thom-heinrich/twinr/src/twinr/agent/personality/README.md

# personality

`personality` owns the typed evolving companion-state layer for `twinr.agent`.
It sits between long-term storage and base-agent prompting: the package defines
structured personality models, translates them into ordered prompt layers, and
now also owns the policy-gated background evolution path that persists signals
and current-state commits through remote-primary state.

## Responsibility

`personality` owns:
- define typed models for stable character, learned conversation style, humor, relationship context, continuity, place/world awareness, and reflection deltas
- build ordered prompt layers that preserve Twinr's legacy `SYSTEM` / `PERSONALITY` / `USER` contract
- mark authority-bearing `SYSTEM` / `PERSONALITY` prompt layers with trusted builder provenance so prompt-authority guards can distinguish them from contextual data
- render a bounded conversational self-expression and `MINDSHARE` layer so Twinr can naturally speak from ongoing themes without pretending to have a human inner life
- derive authoritative per-turn steering cues from shared-thread and appetite state so Twinr can decide more consistently when to briefly update, when one calm follow-up is acceptable, and when it should simply observe
- derive explicit per-topic positive-engagement actions such as `silent`, `hint`, `brief_update`, `ask_one`, and `invite_follow_up` so Twinr can foster welcomed interaction without becoming pushy
- derive calm ambient display-impulse candidates from that same structured state so Twinr's evolving tone, topics, co-attention, and memory-follow-up needs can surface visually outside spoken turns
- correlate shown reserve-card exposures with later structured turn evidence so the right-hand lane can feed back into the same bounded engagement model as spoken conversation
- classify shown-card reactions more precisely, including immediate pickup versus delayed pickup or visible pushback, so Twinr can remember not just whether a card landed but how directly it landed
- serialize those steering cues for runtime evaluators with compact semantic match summaries and region-qualified local titles where available, then resolve matched topics back into concrete follow-up keep-open versus release-after-answer behavior
- provide storage seams for remote current-state loading and saving without pushing persistence into base-agent prompting
- keep prompt-time snapshot reads read-only and current-head-only, so first live turns on the Pi never reopen legacy snapshot or pointer/blob probes on the critical path
- keep explicit prompt-time remote-read caps authoritative across nested current-head helpers, so supervisor/personality prompt loads cannot silently widen a 2-second hot-path budget back to cold bootstrap timeouts
- extract structured interaction, continuity, place, and world signals from long-term consolidation output and tool history
- gate background learning so repeated interaction, place, and world signals can evolve the durable personality snapshot without allowing one-off drift
- expose a narrow public engagement-signal read seam so non-prompt runtime consumers such as the ambient reserve bus can adapt from the same persisted state instead of rebuilding their own engagement view
- expose both synchronous commit paths and foreground-safe queueing paths so runtime turn finalization can hand off tool-history learning without blocking on remote-primary personality writes
- expose one explicit persisted-history probe seam so nightly/runtime operators can distinguish a truly readable zero-delta state from remote-blind or partially unreadable personality history
- manage RSS/Atom subscriptions plus calm refresh/discovery state for place/world intelligence
- learn slow-changing topic/region source-calibration signals from structured conversation and tool evidence
- condense repeated feed updates into situational-awareness threads so world context can mature over days/weeks instead of staying headline-shaped
- decay stale world and relationship context so Twinr stays situationally aware without becoming news-stuck or overfitting old preferences

`personality` does **not** own:
- provider-specific prompt copy or wording
- memory, reminder, automation, or graph persistence implementations
- foreground runtime loop decisions about which dynamic sections belong to tool, supervisor, or main turns
- the fast supervisor lane's final prompt selection and routing policy

## Key files

| File | Purpose |
|---|---|
| [models.py](./models.py) | Typed evolving-personality state and prompt-layer models |
| [_payload_utils.py](./_payload_utils.py) | Shared payload normalization helpers reused by `models.py` and `intelligence/models.py` so remote-state decoding stays aligned |
| [context_builder.py](./context_builder.py) | Ordered prompt-layer assembly |
| [self_expression.py](./self_expression.py) | Conversational self-expression policy plus prompt-facing current-mindshare rendering |
| [_display_utils.py](./_display_utils.py) | Shared text normalization, truncation, and deterministic variation helpers for ambient display copy/candidate generation |
| [display_impulse_copy.py](./display_impulse_copy.py) | Deterministic fallback copy for ambient display impulses that keeps the large headline explanatory and the smaller second line as the CTA when the bounded reserve-lane LLM rewrite is unavailable |
| [display_impulses.py](./display_impulses.py) | Silent ambient display-impulse candidates derived generically from mindshare and positive-engagement state, including structured generation context, semantic `card_intent` blocks for reserve-card rewriting, and a generic candidate-family label for reserve-bus planning mix |
| [ambient_feedback.py](./ambient_feedback.py) | Correlate shown reserve-card exposures with later structured turn evidence and turn those reactions into generic engagement signals |
| [positive_engagement.py](./positive_engagement.py) | Explicit positive-engagement actions derived generically from appetite, ongoing interest, and co-attention |
| [steering.py](./steering.py) | Authoritative turn-steering cues plus runtime follow-up resolution derived from co-attention and conversation appetite |
| [profile_defaults.py](./profile_defaults.py) | Shared baseline style/humor profiles used by the runtime evolution loop and evaluation tooling |
| [_remote_state_utils.py](./_remote_state_utils.py) | Shared remote-primary adapter resolution used by the personality and world-intelligence snapshot stores |
| [store.py](./store.py) | Remote current-head/item persistence seam for personality snapshot state, signals, and deltas; prompt-time loads stay read-only and current-head-only so live voice turns do not reopen legacy snapshot probes |
| [evolution.py](./evolution.py) | Policy-gated background learning loop, contradiction/sensitivity gates, and decay maintenance |
| [signals.py](./signals.py) | Structured signal taxonomy plus extraction for style, humor, topic, continuity, place, and world evidence |
| [learning.py](./learning.py) | Runtime-facing bridge from extracted signals into background evolution |
| [service.py](./service.py) | Prompting-facing integration service plus the public read seam for persisted engagement signals used by the ambient reserve bus; short-lived caches key on stable remote-state identity so capped-timeout clones do not replay the same remote reads every turn |
| [intelligence/](./intelligence) | RSS/world-intelligence subscriptions, calibration signals, reflection-phase recalibration, and refresh-to-world-signal conversion |
| [component.yaml](./component.yaml) | Structured package metadata |
| [AGENTS.md](./AGENTS.md) | Local invariants and verification |

## Usage

```python
from twinr.agent.personality import PersonalityContextService

service = PersonalityContextService()
sections = service.build_static_sections(
    legacy_sections=(("SYSTEM", "Base system"), ("PERSONALITY", "Base style")),
    config=config,
    remote_state=remote_state,
)
```

```python
from twinr.agent.personality import (
    PersonalityLearningService,
)

learning = PersonalityLearningService.from_config(config, remote_state=remote_state)
result = learning.record_tool_history(
    tool_calls=(tool_call,),
    tool_results=(tool_result,),
)
```

```python
learning.enqueue_tool_history(
    tool_calls=(tool_call,),
    tool_results=(tool_result,),
)
# later, one background commit path flushes the queued signals
learning.flush_pending()
```

## Learning model

The current signal taxonomy is intentionally structured and conservative:

- `topic_affinity` and `topic_aversion` shape relationship salience only after repeated support
- `verbosity_preference` and `initiative_preference` update a separate conversation-style profile instead of rewriting core traits
- `humor_feedback` may move humor intensity slowly, but sensitive-context turns never reinforce humor upward implicitly
- `thread` summaries refresh continuity directly and expire over time
- `world` signals are freshness-bound and decay out of the prompt once stale
- RSS-backed world intelligence is separate from ad-hoc live search: discovery is occasional and explicit, calibration learns slowly from structured conversation/tool evidence, refresh is cadence-bound, and feed items become contextual `WORLD`/`CONTINUITY` updates plus slower situational-awareness threads
- Twinr's conversational self-expression stays bounded: it may speak from `MINDSHARE` when the user invites open conversation or asks what Twinr has been following, but it must not invent secret emotions, private off-screen experiences, or human-like inner life
- `MINDSHARE` surfacing stays generic and data-driven: selection may vary slightly via bounded stochasticity, but it must be based on source type and salience rather than hardcoded entity names or place-first special cases
- repeated user engagement with one topic may boost how often matching mindshare items surface and how strongly the RSS intelligence layer continues to watch that topic, but this must remain bounded and evidence-driven
- explicit structured reactions like follow-up requests may raise topic engagement faster than passive affinity, but the signal must stay typed and auditable
- boosted topic engagement must decay over time and let RSS tuning fall back to baseline when the user stops leaning into that topic
- Twinr's engagement model distinguishes `resonant`, `warm`, `uncertain`, `cooling`, and `avoid`; absence alone must not count as dislike unless repeated prior exposure and non-reengagement are structurally evidenced
- topics currently classified as `avoid` must be suppressed from surfaced `MINDSHARE`, not merely scored lower, so explicit back-off signals cannot leak into prompt context
- `MINDSHARE` now also derives a topic-specific `conversation appetite` from those engagement states plus the learned global style profile, so each surfaced theme carries bounded cues for `depth`, `follow-up`, and `proactivity` instead of relying on hidden prompt guesswork
- `positive_engagement.py` lifts that implicit guidance into explicit turn actions: each surfaced topic resolves generically to `silent`, `hint`, `brief_update`, `ask_one`, or `invite_follow_up`, and the policy must stay topic-generic instead of accreting hardcoded examples
- `display_impulses.py` and `display_impulse_copy.py` reuse the same generic state for non-voice ambient display moments: reserve-card candidates must stay positive and generic, with an explanatory headline plus a separate CTA line instead of hardcoding specific places, topics, or benchmark phrases
- the ambient display lane may also surface a fresh continuity thread as one calm `hint` card before durable user engagement has fully formed, because the reserve bus is a lower-pressure surface than a spoken turn; `cooling` and `avoid` topics must still stay out
- reserve-card candidates should stay companion-like rather than search-box-like: raw `live_search` residue may still shape durable engagement state, but it should not surface directly as a visible right-lane opener
- `display_impulses.py` now also carries one generic `candidate_family` plus semantic `card_intent` per reserve-card candidate so the right-hand bus can mix world/place/memory/social families without ad-hoc named-topic spacing rules and the LLM rewrite step can write from structured meaning instead of only phrase-like anchors
- ambient reserve-card copy should make the headline itself explain the topic and use the smaller second line as the CTA, while still carrying one clear topical anchor so the user immediately knows which thread Twinr wants to open
- ambient reserve-card copy may also surface calm memory-improving prompts such as open-thread follow-ups, clarifying questions, or consistency checks, but only when those come from structured durable state rather than ad-hoc string hacks
- reserve-lane generation should receive generic structured context for those memory or shared-thread prompts, so the visible wording can stay natural and personality-shaped instead of echoing raw topic labels
- `self_expression.py` and `display_impulses.py` should hand reserve generation the real thread/topic summary itself, not internal English scaffolding like durable-attention wrappers, so visible German copy can stay grounded in the actual topic instead of paraphrasing implementation noise
- shown reserve cards now participate in the same generic engagement loop: later structured turn evidence may resolve one card into pickup, cooling, aversion, or repeated non-pickup, and those outcomes flow back through the normal personality/world-intelligence evolution path
- immediate shown-card pickup should count as stronger positive evidence than a much later return, and the structured feedback path may also emit a short-lived reserve-bus feedback hint so the same-day display plan can adapt faster without hardcoding topics in the runtime loop
- repeated user returns to a topic may also raise Twinr's persisted `ongoing interest` in it; this is the companion analogue of `stop/linger/return` signals in ranking systems, but bounded for dignity and calm rather than optimized for addiction or time-on-device
- when sustained user interest and Twinr's own feed coverage line up, the system now also tracks bounded `co-attention` so some themes can become genuine shared running threads rather than isolated prompt hints
- `steering.py` turns that same state into authoritative turn guidance inside `PERSONALITY`, serializes compact machine-readable cues for the closure evaluator, and resolves matched topics back into concrete runtime follow-up behavior without turning `MINDSHARE` itself into instruction authority
- steering cues should stay semantically narrow: if a durable signal already says a topic is local/regional and region-scoped, the cue title may carry that regional anchor so closure matching does not confuse nearby community topics with public-policy threads
- the fast supervisor lane should consume only a lean subset of this package: stable character/style may flow there, but volatile layers such as `MINDSHARE`, `CONTINUITY`, `PLACE`, `WORLD`, and `REFLECTION` must stay out so noisy search routing does not get semantically dragged by ambient state

## See also

- [component.yaml](./component.yaml)
- [AGENTS.md](./AGENTS.md)
- [../base_agent/prompting/README.md](../base_agent/prompting/README.md)
- [../../../../docs/persistent_personality_architecture.md](../../../../docs/persistent_personality_architecture.md)
