thom-heinrich/twinr/src/twinr/agent/base_agent/runtime/README.md

# runtime

`runtime` owns the canonical `TwinrRuntime` object for the base agent. It
assembles focused mixins for lifecycle setup, state transitions, provider
context, structured memory, guided user-discovery, reminders and automations,
and runtime snapshot durability.

## Responsibility

`runtime` owns:
- compose `TwinrRuntime` from focused mixins
- bootstrap and shut down runtime-owned stores and services
- honor the configured required-remote readiness contract during bootstrap, including trusting the external watchdog artifact in Pi `watchdog_artifact` mode instead of forcing a second deep remote probe
- drive state transitions for listening, answering, printing, and failures
- rearm follow-up listening directly from `answering` when a conversation stays open after a spoken reply
- also permit the delayed `waiting -> listening` reopen that occurs when speech has already ended but the follow-up closure gate resolves a moment later
- collapse transcript-first provisional `tts_finished + follow_up_rearmed` into one persisted `listening` snapshot when the remote follow-up window is already open, so the visible Pi surface does not pay two back-to-back runtime writes before leaving `answering`
- assemble provider-facing context, adaptive timing, voice guidance, and active guided-discovery state hints for tool-capable turns
- normalize legacy voice-status labels before provider guidance so low-risk discovery turns do not accidentally fall back to conservative unknown-speaker wording
- surface the currently visible reserve-lane card as bounded grounding context for supervisor/search lanes when the user is clearly reacting to what Twinr is showing, including a stronger per-turn authoritative overlay for fast supervisor decisions
- keep the first-word lane on bounded local context so direct replies never block on remote long-term retrieval
- keep the supervisor fast lane on the same remote-free path while still surfacing one local on-device memory summary
- keep runtime-local tool turns on a bounded tiny-recent context when broader long-term memory is not needed, so status/control handoffs do not block the streaming final lane on remote retrieval
- keep tool-context guided-discovery hints on one local prompt-safe status snapshot, so live voice turns never trigger authoritative remote discovery reads just to build a system hint
- emit provider-context stage metrics and one explicit remote-context decision trace when workflow forensics bind runtime trace hooks, so slow `tool_provider_conversation_context()` turns can be attributed to lock snapshot, discovery, long-term retrieval, or final message assembly instead of appearing as one opaque blob
- mediate on-device memory, durable memory, reminders, automations, and snapshots
- expose explicit durable-memory reads from the prompt-context store so later recall of `remember_memory` facts has a runtime-owned read path, not only hidden prompt assembly
- restore persisted runtime status through the state-machine snapshot contract instead of assigning to the read-only runtime `status` property, so startup restore can reinstate only the safe idle `waiting` state plus any orthogonal `printing_active` flag without false warnings while refusing to resurrect stale non-idle or `error` statuses from older process lifetimes
- let `state.RuntimeSnapshotStore` remain the authoritative cross-process snapshot lock so Pi runtimes with `portalocker` installed do not self-deadlock by taking the same lock file twice during restore/persist
- expose reminder-reservation release semantics so workflow races can unwind a reserved reminder before speech starts without forcing a fake failure retry delay
- expose the runtime-side guided user-discovery flow so Twinr can persist, review, correct, and delete high-value get-to-know-you facts across managed context, graph memory, and durable memory without bloating orchestration code
- expose active self-coding dialogue and compile-job guidance to the tool lane so follow-up answers and activation requests can reuse runtime-owned `session_id` / `job_id` state instead of asking the user for internal identifiers
- forward completed tool history into long-term-backed personality learning after a turn is finalized
- keep the explicit best-effort `flush_long_term_memory()` API bounded to the caller's timeout while reserving the stricter remote-primary minimum only for long-term object/graph/midterm durability paths, not already-attested prompt-context writes
- expose runtime-side RSS/world-intelligence configuration so persistent feed subscriptions can shape Twinr's calm place/world awareness
- own the bounded temporary voice-quiet window so Twinr can suppress transcript-first wake and automatic follow-up for a user-requested period without changing the button/manual path

`runtime` does **not** own:
- workflow loops or hardware/audio orchestration
- provider transport or instruction-text assembly
- reminder, automation, graph-memory, or snapshot store implementations
- state-machine definitions outside the runtime-facing methods

## Key files

| File | Purpose |
|---|---|
| [runtime.py](./runtime.py) | Compose `TwinrRuntime` |
| [base.py](./base.py) | Bootstrap services and shutdown |
| [flow.py](./flow.py) | Drive turn and print flow |
| [context.py](./context.py) | Build provider and timing context |
| [discovery.py](./discovery.py) | Runtime bridge for the guided user-discovery service |
| [self_coding.py](./self_coding.py) | Runtime bridge for active self-coding dialogue and compile-job guidance |
| [display_grounding.py](./display_grounding.py) | Read the active reserve-lane cue and turn it into bounded provider-grounding messages plus an authoritative per-turn supervisor overlay |
| [memory.py](./memory.py) | Mutate structured and durable memory |
| [automation.py](./automation.py) | Manage reminders and automations, including releasing reserved reminders when delivery is aborted before output starts |
| [voice_quiet.py](./voice_quiet.py) | Runtime-owned temporary voice-quiet window state |
| [snapshot.py](./snapshot.py) | Persist and restore runtime state |
| [component.yaml](./component.yaml) | Structured package metadata |

## Usage

```python
from twinr.agent.base_agent import TwinrConfig, TwinrRuntime

runtime = TwinrRuntime(config=TwinrConfig())
runtime.begin_listening(request_source="button", button="green")
runtime.submit_transcript("Bitte erinnere mich morgen an meine Tabletten.")
runtime.complete_agent_turn("Ich erinnere dich morgen daran.")
runtime.rearm_follow_up()
runtime.shutdown(timeout_s=1.0)
```

## See also

- [component.yaml](./component.yaml)
- [AGENTS.md](./AGENTS.md)
- [conversation](../conversation/README.md)
- [state](../state/README.md)
- [realtime_runner.py](../../workflows/realtime_runner.py)
