thom-heinrich/twinr/docs/longterm_memory.md

# Long-Term Memory Architecture

Twinr's long-term memory runtime path now lives under `src/twinr/memory/longterm/`.

The current target-state architecture for a frontier-grade Twinr memory system is documented separately in:

- `src/twinr/memory/longterm/MEMORY_ARCHITECTURE.md`

This layer keeps long-term memory responsibilities separated from:

- `src/twinr/memory/on_device/` for short rolling conversation memory
- `src/twinr/memory/context_store.py` for durable markdown/profile stores
- `src/twinr/memory/chonkydb/` for ChonkyDB client, graph schema, and personal graph logic
- `src/twinr/agent/base_agent/runtime/` for turn orchestration

## Package split

- package root:
  - `__init__.py` provides the stable public API
  - `MEMORY_ARCHITECTURE.md` documents the target-state design
- `core/`
  - immutable runtime and versioned long-term memory object models plus ontology helpers
- `ingestion/`
  - cautious turn, proposition, multimodal, and sensor-memory extraction paths
- `reasoning/`
  - truth maintenance, consolidation, reflection, conflicts, and retention policy
- `retrieval/`
  - hybrid retrieval, bounded provider context assembly, and silent subtext building
- `storage/`
  - structured persistence, mid-term packet storage, and remote-primary snapshot access
- `proactive/`
  - proactive planning plus reservation, cooldown, and delivery-history state
- `runtime/`
  - orchestration surface and bounded background writers
- `evaluation/`
  - synthetic, multimodal, and subtext-focused eval harnesses
- `../query_normalization.py`
  - canonical retrieval query rewriting plus low-information token filtering for multilingual memory lookup

## Current runtime behavior

When enabled, Twinr uses the long-term service in two directions:

1. Before a provider call, it builds a structured long-term context package:
   - silent personalization subtext
   - mid-term continuity packets
   - recent episodic memories
   - graph-based personalization context
   - conflict clarification context when relevant
2. After a normal conversation turn finishes, it can queue an episodic memory write in the background.
   - the live extractor now uses a two-stage path:
     - structured proposition extraction
     - deterministic compilation into versioned long-term objects and graph edges
3. During live operation, it can also queue multimodal evidence from:
   - PIR/camera sensor observations
   - green/yellow button usage
   - completed print deliveries
   - live camera captures
4. When enabled, it can compile bounded sensor-memory routine and deviation objects from repeated multimodal pattern evidence.
5. When enabled, the background loops can reserve one bounded long-term proactive candidate at a time, apply cooldown/sensitivity policy, and speak it through the existing proactive prompt path.

The service keeps semantic memory text in canonical English. Names, phone numbers, email addresses, IDs, and verbatim quoted text stay unchanged.

For non-English user queries, the retrieval path can build a short canonical English retrieval query before ranking memories. This keeps memory content English without relying on brittle per-language prompt rules in the prompt builder.

## Current storage split

- recent episodic long-term memories:
  - `state/MEMORY.md`
- compiled mid-term packets:
  - `TWINR_LONG_TERM_MEMORY_PATH/twinr_memory_midterm_v1.json`
- local graph-backed long-term structures:
  - `TWINR_LONG_TERM_MEMORY_PATH/twinr_graph_v1.json`
- archived long-term objects:
  - `TWINR_LONG_TERM_MEMORY_PATH/twinr_memory_archive_v1.json`

When `TWINR_LONG_TERM_MEMORY_MODE=remote_primary`, these local files become cache/migration artifacts. ChonkyDB is then the primary long-term source, and the stores read/write snapshot state through the remote backend before updating the local cache.

If remote-primary memory is required and ChonkyDB is unavailable, Twinr falls back only to simple conversation memory (`MEMORY.md`, recent turns, personality/user context). In that mode, long-term graph/fact/midterm retrieval is withheld instead of silently pretending to be available.

## Config

- `TWINR_LONG_TERM_MEMORY_ENABLED`
- `TWINR_LONG_TERM_MEMORY_BACKEND`
- `TWINR_LONG_TERM_MEMORY_MODE`
- `TWINR_LONG_TERM_MEMORY_REMOTE_REQUIRED`
- `TWINR_LONG_TERM_MEMORY_PATH`
- `TWINR_LONG_TERM_MEMORY_BACKGROUND_STORE_TURNS`
- `TWINR_LONG_TERM_MEMORY_WRITE_QUEUE_SIZE`
- `TWINR_LONG_TERM_MEMORY_RECALL_LIMIT`
- `TWINR_LONG_TERM_MEMORY_QUERY_REWRITE_ENABLED`
- `TWINR_LONG_TERM_MEMORY_REMOTE_READ_TIMEOUT_S`
- `TWINR_LONG_TERM_MEMORY_REMOTE_WRITE_TIMEOUT_S`
- `TWINR_LONG_TERM_MEMORY_TURN_EXTRACTOR_MODEL`
- `TWINR_LONG_TERM_MEMORY_TURN_EXTRACTOR_MAX_OUTPUT_TOKENS`
- `TWINR_LONG_TERM_MEMORY_MIDTERM_ENABLED`
- `TWINR_LONG_TERM_MEMORY_MIDTERM_LIMIT`
- `TWINR_LONG_TERM_MEMORY_REFLECTION_WINDOW_SIZE`
- `TWINR_LONG_TERM_MEMORY_REFLECTION_COMPILER_ENABLED`
- `TWINR_LONG_TERM_MEMORY_REFLECTION_COMPILER_MODEL`
- `TWINR_LONG_TERM_MEMORY_REFLECTION_COMPILER_MAX_OUTPUT_TOKENS`
- `TWINR_LONG_TERM_MEMORY_SUBTEXT_COMPILER_ENABLED`
- `TWINR_LONG_TERM_MEMORY_SUBTEXT_COMPILER_MODEL`
- `TWINR_LONG_TERM_MEMORY_SUBTEXT_COMPILER_MAX_OUTPUT_TOKENS`
- `TWINR_LONG_TERM_MEMORY_PROACTIVE_ENABLED`
- `TWINR_LONG_TERM_MEMORY_PROACTIVE_POLL_INTERVAL_S`
- `TWINR_LONG_TERM_MEMORY_PROACTIVE_MIN_CONFIDENCE`
- `TWINR_LONG_TERM_MEMORY_PROACTIVE_REPEAT_COOLDOWN_S`
- `TWINR_LONG_TERM_MEMORY_PROACTIVE_SKIP_COOLDOWN_S`
- `TWINR_LONG_TERM_MEMORY_PROACTIVE_RESERVATION_TTL_S`
- `TWINR_LONG_TERM_MEMORY_PROACTIVE_ALLOW_SENSITIVE`
- `TWINR_LONG_TERM_MEMORY_PROACTIVE_HISTORY_LIMIT`
- `TWINR_LONG_TERM_MEMORY_SENSOR_MEMORY_ENABLED`
- `TWINR_LONG_TERM_MEMORY_SENSOR_BASELINE_DAYS`
- `TWINR_LONG_TERM_MEMORY_SENSOR_MIN_DAYS_OBSERVED`
- `TWINR_LONG_TERM_MEMORY_SENSOR_MIN_ROUTINE_RATIO`
- `TWINR_LONG_TERM_MEMORY_SENSOR_DEVIATION_MIN_DELTA`
- `TWINR_LONG_TERM_MEMORY_RETENTION_ENABLED`
- `TWINR_LONG_TERM_MEMORY_RETENTION_MODE`
- `TWINR_LONG_TERM_MEMORY_RETENTION_RUN_INTERVAL_S`
- `TWINR_LONG_TERM_MEMORY_ARCHIVE_ENABLED`
- `TWINR_LONG_TERM_MEMORY_MIGRATION_ENABLED`
- `TWINR_LONG_TERM_MEMORY_MIGRATION_BATCH_SIZE`
- `TWINR_CHONKYDB_BASE_URL`
- `TWINR_CHONKYDB_API_KEY`
- `TWINR_CHONKYDB_API_KEY_HEADER`
- `TWINR_CHONKYDB_ALLOW_BEARER_AUTH`
- `TWINR_CHONKYDB_TIMEOUT_S`

## Design constraints

- retrieval must stay deterministic and small
- response generation must not block on background memory persistence
- persistent writes must fail clearly instead of silently mutating state
- memory context should influence tone and personalization only when relevant
- hidden memory should usually shape replies silently instead of being announced explicitly
- the user-facing reply language stays independent from the internal memory language

By default, the long-term path should stay project-local under `state/chonkydb` so temporary runs and secondary env files do not leak graph data into a shared `/twinr` tree. Remote-primary mode does not change that local path; it changes which backend is treated as the source of truth.

## Synthetic eval

Twinr now also carries a deterministic synthetic long-term memory eval harness under `src/twinr/memory/longterm/eval.py`.

The current harness seeds:

- 500 synthetic memories
- 50 dialogue/eval cases

Covered case families:

- exact contact recall
- contact disambiguation
- shopping recall
- temporal multihop recall
- episodic conversation recall

Repro:

```bash
PYTHONPATH=src ./.venv/bin/python -m twinr.memory.longterm.evaluation.eval
```

## Response-level subtext eval

Twinr also carries a bounded live response eval for the silent personalization layer under `src/twinr/memory/longterm/evaluation/subtext_eval.py`.

This eval uses real generated replies and checks whether hidden personal context is woven into answers naturally instead of being announced explicitly.
It runs with isolated per-case base instructions so unrelated repo personality or user files do not pollute the measurement.

When `TWINR_LONG_TERM_MEMORY_SUBTEXT_COMPILER_ENABLED=true`, the response path first compiles relevant graph and episodic memory into a bounded structured subtext program, then injects that compiled program as the silent personalization system message for the turn.

Current case families:

- preference-based personalization
- situational continuity
- social-role familiarity
- episodic continuity
- irrelevant-query controls

Repro:

```bash
PYTHONPATH=src ./.venv/bin/python -m twinr.memory.longterm.evaluation.subtext_eval
```

Current validated run on 2026-03-15:

- 8/8 passed
- 0 explicit memory-announcement violations
- average naturalness score: 4.875/5

Current status:

- situational continuity, social-role familiarity, episodic continuity, preference shaping, and irrelevant-query controls are all green on Pi validation

## Multimodal goldset eval

Twinr also carries a deterministic multimodal long-term eval under `src/twinr/memory/longterm/evaluation/multimodal_eval.py`.

This harness seeds a realistic mixed store with:

- 200 multimodal device events
- 300 episodic conversation turns
- 50 fixed goldset cases over presence, button/print routine, camera interaction, combined episodic+multimodal context, and irrelevant-query controls

It exercises the full provider-context path with canonical-English retrieval queries, rather than checking only raw extractor outputs.

The fixture day is anchored relative to the run date so the conversation-turn
half remains inside the active episodic-retention window; the goldset should
not drift red just because the wall clock moved past a hard-coded calendar day.

Repro:

```bash
PYTHONPATH=src ./.venv/bin/python -m twinr.memory.longterm.evaluation.multimodal_eval
```

Current validated run on 2026-04-04:

- 500 seeded entries
- 50/50 cases passed
- 1.0 accuracy

This eval also guards against two subtle quality regressions:

- internal machine metadata like `slot_key` or `support_count` leaking into retrieval ranking
- irrelevant episodic fallback context appearing on unrelated user questions

## Messy mixed-corpus eval

Twinr also carries one larger remote-memory stress eval under
`src/twinr/memory/longterm/evaluation/messy_memory_eval.py`.

This harness intentionally combines the existing fixed fixtures into one shared
remote namespace instead of running them in isolation:

- the synthetic recall corpus (`500` seeded entries, `50` cases)
- the multimodal routine corpus (`500` seeded entries, `50` cases)
- the expanded unified-retrieval goldset (`50` natural-language cases)

The purpose is different from the individual suites: it measures whether the
same recall quality still holds once graph contacts, plans, preferences,
episodic turns, multimodal routines, durable conflicts, graph joins, and
midterm packets all coexist in the same ChonkyDB namespace.

It also runs both phases:

- `writer`
  - immediately after seeding the messy corpus
- `fresh_reader`
  - from a separate isolated runtime root against the same remote namespace

That makes restart regressions visible with explicit case-level deltas instead
of only one blended score.

During the scored phases the harness disables optional query-rewrite and
subtext-compiler LLM lanes and skips materialized provider-answer-front
persisting, because the goal is to measure ChonkyDB-backed memory recall and
precision rather than auxiliary rewrite/cache latency.

Covered dimensions in the shared corpus:

- exact contact lookup
- contact disambiguation
- shopping recall
- temporal multihop recall
- episodic conversation recall
- multimodal presence routine recall
- button / print routine recall
- camera interaction recall
- combined episodic + multimodal context
- negative controls / irrelevant-query containment
- unified source/id/join/access-path precision and recall across adaptive, conflict, durable, episodic, graph, and midterm sources
- writer vs fresh-reader restart drift

Repro:

```bash
PYTHONPATH=src ./.venv/bin/python -m twinr.memory.longterm.evaluation.messy_memory_eval --env-file .env --unified-case-profile expanded
```

Artifacts:

- rolling ops artifact:
  - `artifacts/stores/ops/messy_memory_eval.json`
- per-run snapshot:
  - `artifacts/reports/messy_memory_eval/`

## Structured persistence

The long-term service now keeps a local structured store alongside the markdown episodic path.

- structured memory objects:
  - `TWINR_LONG_TERM_MEMORY_PATH/twinr_memory_objects_v1.json`
- compiled mid-term packets:
  - `TWINR_LONG_TERM_MEMORY_PATH/twinr_memory_midterm_v1.json`
- unresolved conflicts:
  - `TWINR_LONG_TERM_MEMORY_PATH/twinr_memory_conflicts_v1.json`

The async background path can now:

1. persist the old markdown episodic turn
2. extract structured memory candidates from the same turn
3. consolidate them against existing structured memory
4. persist durable objects and unresolved conflicts for later retrieval
5. run a bounded reflection pass to strengthen repeated evidence, emit `summary` objects with `summary_type=thread`, and compile a small mid-term packet layer for near-term continuity
6. expose a bounded proactive planner over structured memory for reminders and gentle follow-ups
7. apply bounded retention so old episodes/observations do not accumulate without bound and past events become `expired`

The long-term service can now also surface queued clarification conflicts with concrete answer options and apply explicit resolutions. When a user confirms which memory is correct, Twinr keeps provenance and updates the competing memory states instead of silently overwriting them.

Alongside conflict resolution, the long-term layer now also supports direct review and manual memory hygiene in the same structured store:

- review durable memory objects without dragging unrelated episodic noise into the result set
- confirm a memory as user-validated
- invalidate a memory without deleting provenance
- delete a memory and clean dangling conflict/reference fields

These are currently memory-layer APIs on `LongTermMemoryService` / `LongTermStructuredStore`, so they are available for future portal and voice-tool wiring without inventing a second correction path.

The realtime voice tool path now exposes this explicitly through:

- `get_memory_conflicts`
  - inspect queued conflict questions and option IDs
- `resolve_memory_conflict`
  - activate the chosen option for a slot after spoken clarification

This keeps spoken clarification generic across contacts, preferences, routines, and other slot-based long-term facts instead of hard-coding one-off disambiguation cases.

Multimodal evidence uses the same consolidation/reflection/retention path as conversation turns, but starts from lower-confidence pattern candidates. This lets repeated PIR, camera, button, and printer signals strengthen into durable memory without over-trusting one isolated device event.

On top of those raw multimodal patterns, Twinr can now also compile a bounded sensor-memory layer with:

- presence routines by daypart and weekday/weekend class
- interaction routines such as conversation start, print, camera use, and camera-showing
- same-day low-presence deviation summaries that still require live confirmation before any spoken use

The proactive planner can now turn that layer into bounded routine-aware candidates such as `routine_check_in`, `routine_camera_offer`, and `routine_print_offer`, but only when current live sensor facts confirm the moment is actually suitable.

Live long-term proactive prompts now sit behind a separate reservation/policy layer instead of letting the planner speak directly. That layer is responsible for:

- minimum confidence gating
- sensitivity blocking unless explicitly enabled
- repeat cooldown after successful delivery
- skip cooldown after recent failure/suppression
- short reservation TTL so a stale reserved candidate does not loop forever after crashes
- small durable history under `TWINR_LONG_TERM_MEMORY_PATH/twinr_memory_proactive_state_v1.json`

This keeps the planner pure and keeps live delivery behavior configurable without coupling policy to retrieval or extraction.
