thom-heinrich/twinr/docs/AI_CAMERA_FINE_HAND_GESTURE_PATH.md

# AI Camera Fine Hand Gesture Path

## Purpose

This note evaluates a realistic local path for Twinr to add
`fine_hand_gesture` support on top of the existing Raspberry Pi AI Camera path.

The target class is:
- `thumbs_up`
- `thumbs_down`
- `peace_sign`

This document is deliberately separate from the main camera contract. The
current V1 camera path must stay defensible without pretending that coarse
pose-only output can already support finger-level semantics.

## Current Reality In Twinr

The current Twinr camera stack already has:
- local-first IMX500 person detection
- coarse body pose
- coarse motion
- coarse arm gestures
- stable social-camera snapshot and event surfaces

The current stack now has:
- a dedicated local MediaPipe hand-landmark ROI worker under `src/twinr/hardware/hand_landmarks.py`
- a local MediaPipe Gesture Recognizer path for built-in hand classes
- a bounded custom-gesture workflow under `hardware/piaicam/` for dataset
  capture plus `.task` training/export
- runtime wiring for an optional custom gesture recognizer asset via
  `TWINR_PROACTIVE_LOCAL_CAMERA_MEDIAPIPE_CUSTOM_GESTURE_MODEL_PATH`

The current stack still does **not** have:
- a checked-in product-grade custom `.task` for `thumbs_up`, `thumbs_down`, and `peace_sign`
- enough real household data yet to call that three-gesture live-HCI model production-ready

Environment observations from the current workspace:
- repo-local `.venv` on the leading checkout does **not** currently have `mediapipe`
- the Pi runtime `.venv` on `/twinr` **does** have `mediapipe 0.10.18`
- the Pi runtime has both `HandLandmarker` and `GestureRecognizer` APIs available
- no `*.task` hand/gesture model assets were found under `/twinr`

## Official Source Signals

MediaPipe official sources indicate:
- the Hand Landmarker path is an on-device vision task intended to return hand landmarks
- the Gesture Recognizer task has live-stream support and task APIs suitable for on-device use
- Google provides an official customization path for gesture recognizers based on hand-landmark extraction

Raspberry Pi official sources indicate:
- the AI Camera on IMX500 supports deploying custom neural network models
- Raspberry Pi officially supports pre-packaged and custom IMX500 models through the documented packaging/conversion toolchain

## Candidate Paths

### Option A: MediaPipe Hand Landmarker On The Pi CPU

Use the existing AI-camera person/pose path as the cheap always-on gate. When
Twinr sees a plausible near-device hand or coarse-arm intent, crop one or two
hand candidate ROIs locally and run MediaPipe Hand Landmarker on the Pi CPU.

Pros:
- strongest near-term path for actual finger-level landmarks
- already partially de-risked because `mediapipe` is present on the Pi runtime
- keeps the current IMX500 path for cheap always-on gating
- clean separation: coarse always-on vision stays on IMX500, fine hand analysis
  runs only on demand

Cons:
- adds a second local vision runtime path
- needs ROI extraction and bounded scheduling
- needs model assets to be added and versioned deliberately

Assessment:
- best practical V2 path

### Option B: MediaPipe Gesture Recognizer On The Pi CPU

Use the higher-level Gesture Recognizer task instead of only landmarks.

Pros:
- official on-device task
- faster path to a working canned gesture surface

Cons:
- canned gestures still do not become Pi-specific just because Twinr filters the
  output set
- `peace_sign` remains too brittle on the real device unless Twinr trains for
  the exact user distance, framing, and lighting
- less transparent than working directly from landmarks

Assessment:
- useful as a bootstrap, but likely not enough by itself for Twinr's desired
  label set

### Option C: Custom IMX500 Fine-Hand Model

Train and package a custom model for the AI Camera itself.

Pros:
- best long-term efficiency if fine-hand gestures become a first-class,
  always-on requirement
- keeps more inference work on the camera sensor

Cons:
- highest implementation cost
- requires dataset, training, quantization, conversion, packaging, and Pi-side
  post-processing
- much slower iteration loop than CPU-side landmarks

Assessment:
- attractive later, but wrong first step for Twinr right now

## Recommendation

Recommended path:
1. Keep IMX500 as the always-on coarse gate.
2. Keep one bounded hand-first `LIVE_STREAM` Gesture Recognizer path for the
   user-facing Pi HCI lane.
3. Train a product-specific custom model for exactly `thumbs_up`,
   `thumbs_down`, `peace_sign`, and `none`.
4. Use ROI hand-landmark work only as bounded rescue/context, not as the main
   symbol-decision path.

Why this is the right cut:
- it is local-first
- it matches the current Pi environment
- it keeps the always-on runtime cheap
- it avoids lying about finger semantics on top of a shoulder/elbow/wrist model

## Suggested V2 Architecture

- `src/twinr/hardware/hand_landmarks.py`
  - own the local MediaPipe runtime, task loading, ROI execution, and bounded
    inference API
- `src/twinr/perception/hand_gesture/`
  - own landmark-to-gesture classification and confidence rules
- `src/twinr/proactive/social/local_camera_provider.py`
  - stay thin; only map outputs onto the social contract
- `src/twinr/proactive/social/camera_surface.py`
  - stabilize `fine_hand_gesture` and expose bounded events

## Immediate Follow-Up

The next concrete experiment should be:
- capture a real household dataset with
  `hardware/piaicam/capture_custom_gesture_dataset.py`
- train/export a first custom `.task` with
  `hardware/piaicam/train_custom_gesture_model.py`
- validate `thumbs_up`, `thumbs_down`, and `peace_sign` accuracy on the real Pi
  runtime before treating them as product-grade signals

## Sources

- Google AI Edge, MediaPipe Gesture Recognizer API:
  https://ai.google.dev/edge/mediapipe/api/solutions/python/mp/tasks/vision/GestureRecognizerOptions
- Google AI Edge, gesture recognizer customization guide:
  https://ai.google.dev/edge/mediapipe/solutions/customization/gesture_recognizer
- Raspberry Pi official AI Camera documentation:
  https://www.raspberrypi.com/documentation/accessories/ai-camera.html
