thom-heinrich/twinr/src/twinr/hardware/servo_follow_impl/constants.py

"""Define default values and hard limits for attention-servo follow."""

from __future__ import annotations

_DEFAULT_SERVO_FREQUENCY_HZ = 50
_DEFAULT_SERVO_DRIVER = "auto"
_DEFAULT_TARGET_HOLD_S = 1.1
_DEFAULT_LOSS_EXTRAPOLATION_S = 0.8
_DEFAULT_LOSS_EXTRAPOLATION_GAIN = 0.65
_DEFAULT_MIN_CONFIDENCE = 0.58
_DEFAULT_DEADBAND = 0.045
_DEFAULT_MIN_PULSE_WIDTH_US = 1050
_DEFAULT_CENTER_PULSE_WIDTH_US = 1500
_DEFAULT_MAX_PULSE_WIDTH_US = 1950
_DEFAULT_MAX_STEP_US = 45
_DEFAULT_TARGET_SMOOTHING_S = 0.9
_DEFAULT_MAX_VELOCITY_US_PER_S = 80.0
_DEFAULT_MAX_ACCELERATION_US_PER_S2 = 220.0
_DEFAULT_MAX_JERK_US_PER_S3 = 900.0
_DEFAULT_REST_MAX_VELOCITY_US_PER_S = 35.0
_DEFAULT_REST_MAX_ACCELERATION_US_PER_S2 = 120.0
_DEFAULT_REST_MAX_JERK_US_PER_S3 = 450.0
_DEFAULT_MIN_COMMAND_DELTA_US = 8
_DEFAULT_VISIBLE_RETARGET_TOLERANCE_US = 40
_DEFAULT_VISIBLE_RETARGET_COOLDOWN_S = 0.0
_DEFAULT_REFERENCE_INTERVAL_S = 0.2
_DEFAULT_SOFT_LIMIT_MARGIN_US = 70
_DEFAULT_IDLE_RELEASE_S = 1.0
_DEFAULT_SETTLED_RELEASE_S = 0.0
_DEFAULT_FOLLOW_EXIT_ONLY = False
_DEFAULT_VISIBLE_RECENTER_INTERVAL_S = 30.0
_DEFAULT_VISIBLE_RECENTER_CENTER_TOLERANCE = 0.12
_DEFAULT_MECHANICAL_RANGE_DEGREES = 270.0
_DEFAULT_EXIT_FOLLOW_MAX_DEGREES = 60.0
_DEFAULT_EXIT_ACTIVATION_DELAY_S = 0.75
_DEFAULT_EXIT_SETTLE_HOLD_S = 0.6
_DEFAULT_EXIT_REACQUIRE_CENTER_TOLERANCE = 0.08
_DEFAULT_EXIT_VISIBLE_EDGE_THRESHOLD = 0.62
_DEFAULT_EXIT_VISIBLE_BOX_EDGE_THRESHOLD = 0.92
_DEFAULT_EXIT_COOLDOWN_S = 30.0
_DEFAULT_CONTROL_MODE = "position"
_DEFAULT_STATE_PATH = "state/attention_servo_state.json"
_DEFAULT_ESTIMATED_ZERO_MAX_UNCERTAINTY_DEGREES = 15.0
_DEFAULT_ESTIMATED_ZERO_SETTLE_TOLERANCE_DEGREES = 1.0
_DEFAULT_ESTIMATED_ZERO_SPEED_SCALE = 0.5
_DEFAULT_CONTINUOUS_MAX_SPEED_DEGREES_PER_S = 120.0
_DEFAULT_CONTINUOUS_SLOW_ZONE_DEGREES = 45.0
_DEFAULT_CONTINUOUS_STOP_TOLERANCE_DEGREES = 4.0
_DEFAULT_CONTINUOUS_MIN_SPEED_PULSE_DELTA_US = 70
_DEFAULT_CONTINUOUS_MAX_SPEED_PULSE_DELTA_US = 160
_DEFAULT_ESTIMATED_ZERO_MOVE_PULSE_DELTA_US = _DEFAULT_CONTINUOUS_MIN_SPEED_PULSE_DELTA_US
_DEFAULT_ESTIMATED_ZERO_MOVE_PERIOD_S = 0.8
_DEFAULT_ESTIMATED_ZERO_MOVE_DUTY_CYCLE = 0.2
_DEFAULT_CONTINUOUS_RETURN_TO_ZERO_AFTER_S = 0.0
_MIN_RELEASE_TOLERANCE_US = 12
_MAX_RELEASE_TOLERANCE_US = 48
_SERVO_PRECHECK_TIMEOUT_S = 2.0
_RECOVERABLE_SERVO_FAULT_RETRY_S = 1.0
_CONFLICTING_GPIO_OVERLAY_NAMES = frozenset({"pwm-pio"})
_MOVEMENT_JOURNAL_MAX_SEGMENTS = 256
_MOVEMENT_JOURNAL_MIN_DURATION_S = 0.005
